securelyfitz/USBSanitizer/Hushcon East/img/bbb.png

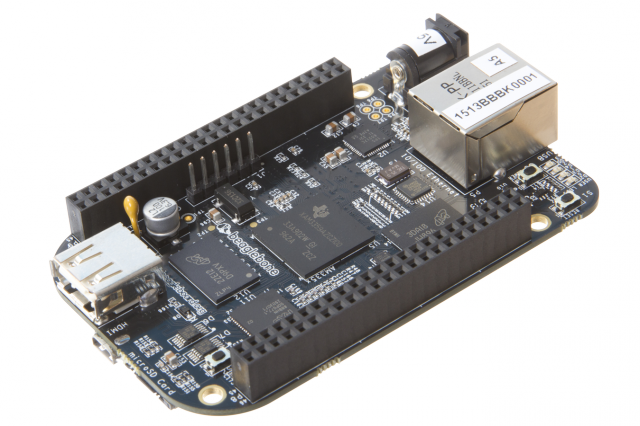
Hushcon East/img/bbb.png
