securelyfitz/USBSanitizer/Hushcon East/img/charts.png

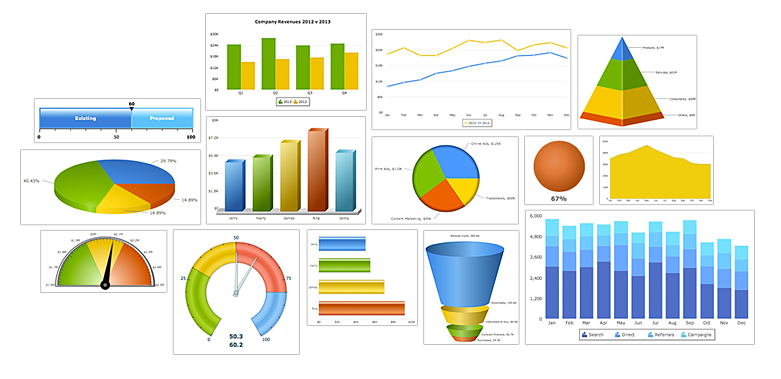
Hushcon East/img/charts.png
