securelyfitz/USBSanitizer/Hushcon East/img/clock.png

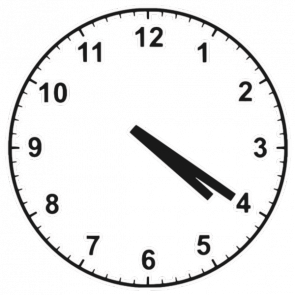
Hushcon East/img/clock.png
