securelyfitz/USBSanitizer/Hushcon East/img/ducky.png

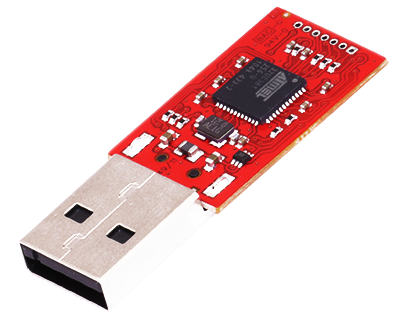
Hushcon East/img/ducky.png
