securelyfitz/USBSanitizer/Hushcon East/img/FSA9280A.png

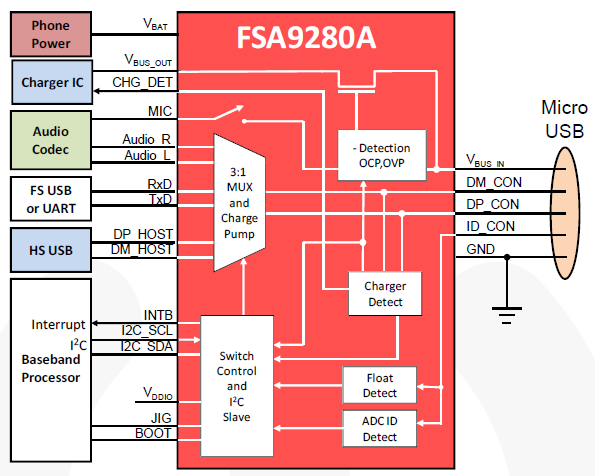
Hushcon East/img/FSA9280A.png
