securelyfitz/USBSanitizer/Hushcon East/img/ftdi.png

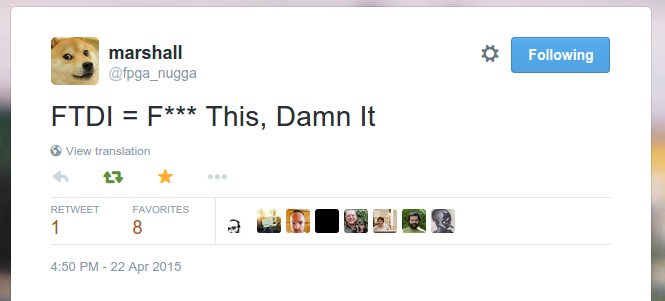
Hushcon East/img/ftdi.png
