securelyfitz/USBSanitizer/Hushcon East/img/ftdiflash.png

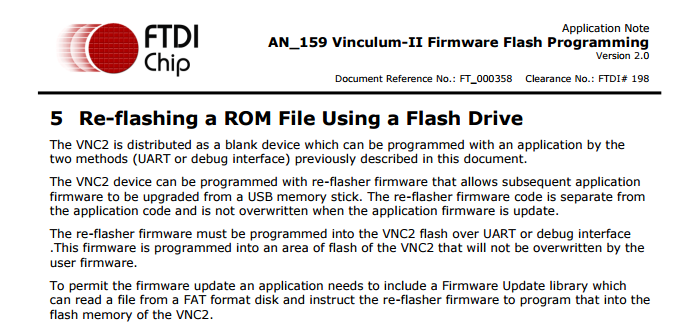
Hushcon East/img/ftdiflash.png
