securelyfitz/USBSanitizer/Hushcon East/img/lnk.png

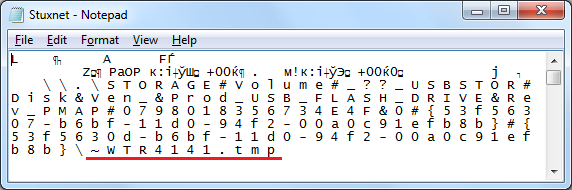
Hushcon East/img/lnk.png
