securelyfitz/USBSanitizer/Hushcon East/img/mac-boot-screen.jpg

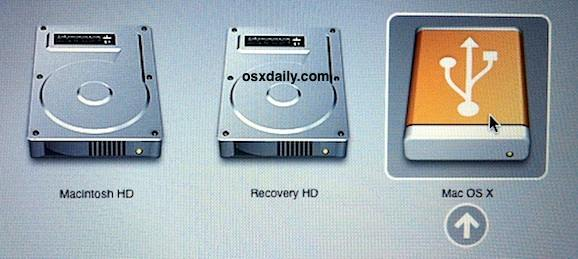
Hushcon East/img/mac-boot-screen.jpg
