securelyfitz/USBSanitizer/Hushcon East/img/nuc.png

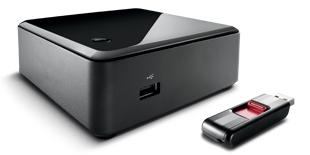
Hushcon East/img/nuc.png
