securelyfitz/USBSanitizer/Hushcon East/img/pic32.png

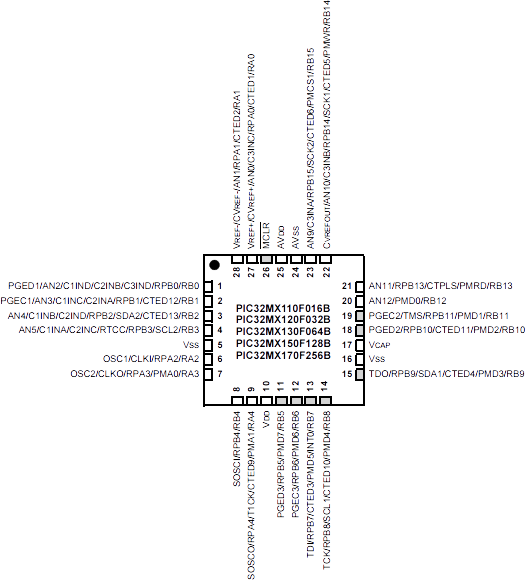
Hushcon East/img/pic32.png
