securelyfitz/USBSanitizer/Hushcon East/img/pogoplug.png

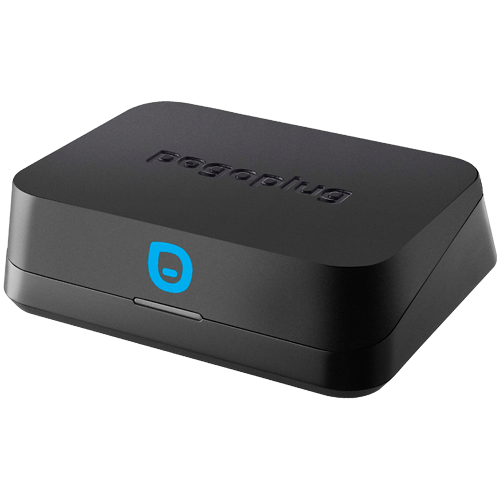
Hushcon East/img/pogoplug.png
