securelyfitz/USBSanitizer/Hushcon East/img/securedrop.png

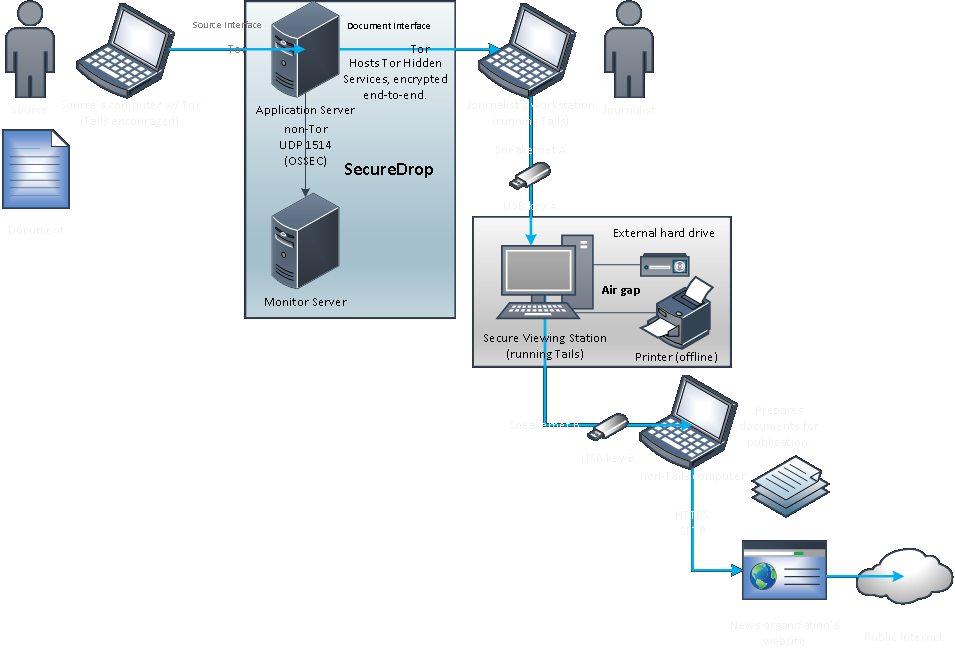
Hushcon East/img/securedrop.png
