securelyfitz/USBSanitizer/Hushcon East/img/training.jpg

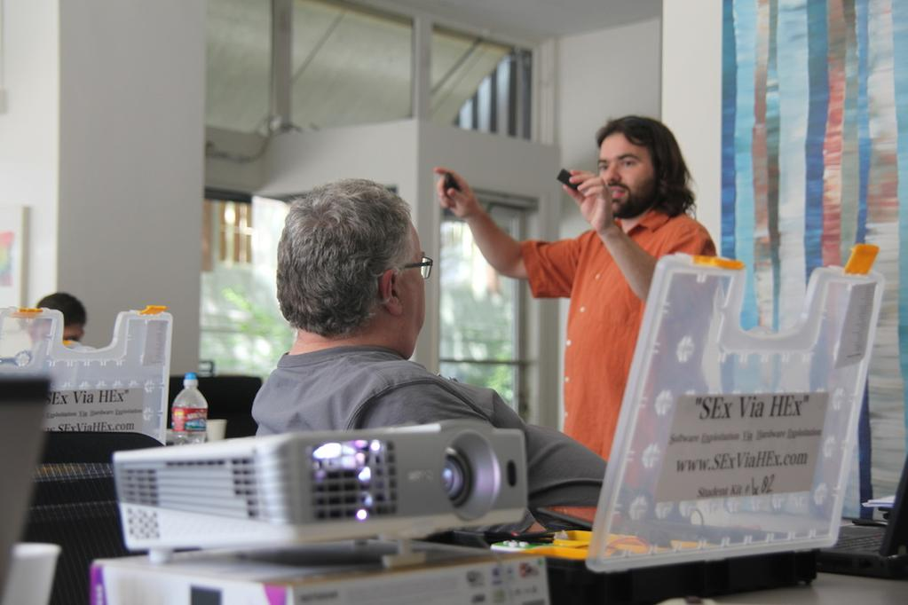
Hushcon East/img/training.jpg
