securelyfitz/USBSanitizer/Hushcon East/img/usbkiller.jpg

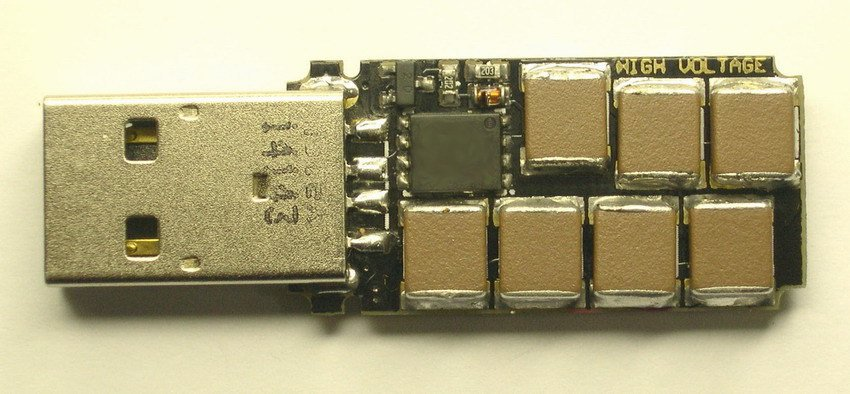
Hushcon East/img/usbkiller.jpg
