securelyfitz/USBSanitizer/Hushcon East/img/usbkiller.png

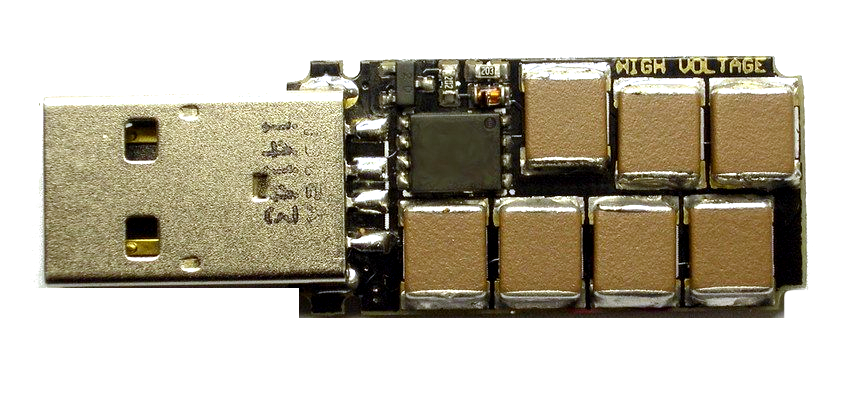
Hushcon East/img/usbkiller.png
