securelyfitz/USBSanitizer/Hushcon East/img/usbsanitizer.png

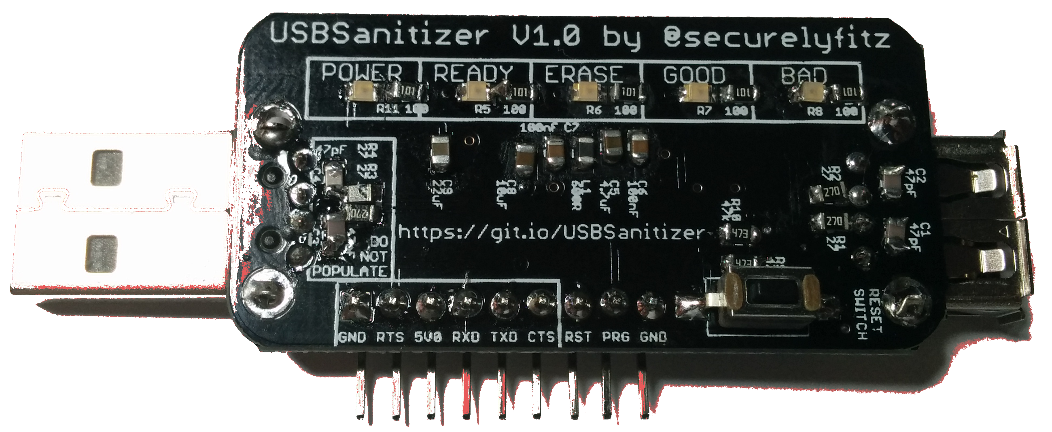
Hushcon East/img/usbsanitizer.png
