securelyfitz/USBSanitizer/Hushcon East/img/usbtrash.jpg

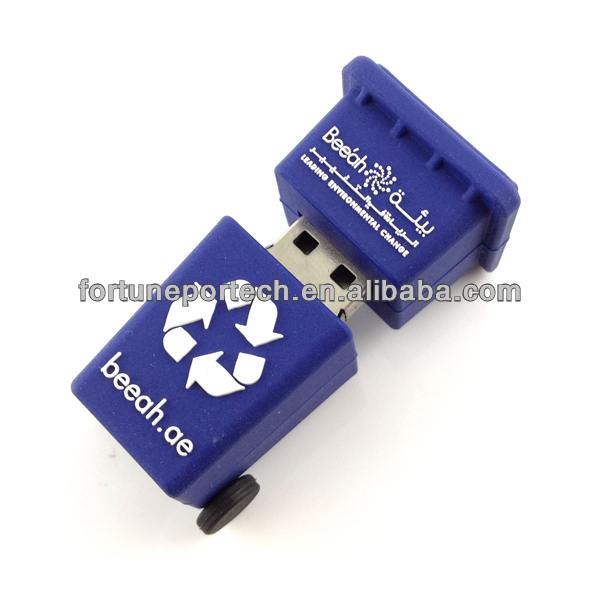
Hushcon East/img/usbtrash.jpg
