securelyfitz/USBSanitizer/Hushcon East/img/vnctools.png

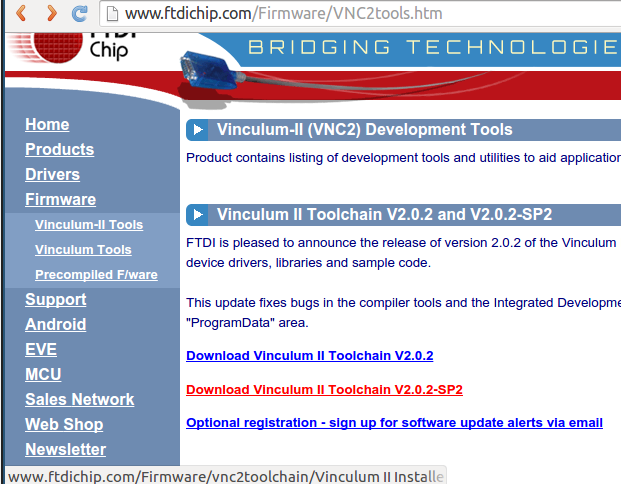
Hushcon East/img/vnctools.png
